RenanG0mes/GamepadPi/General pictures/1.jpg

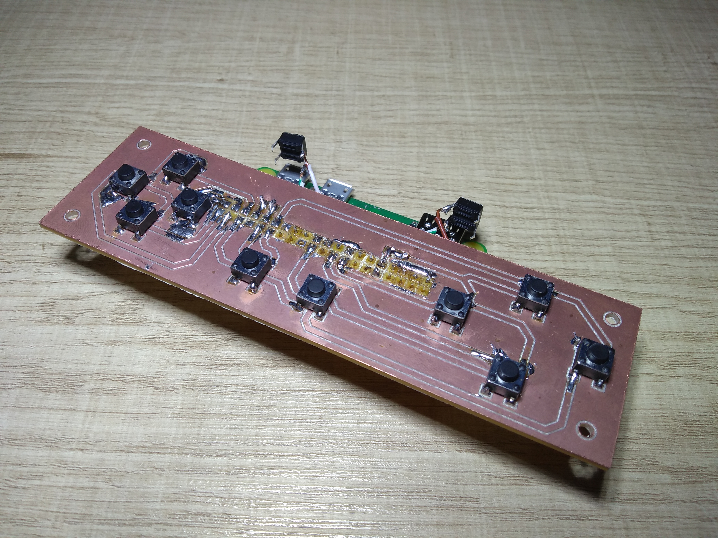
General pictures/1.jpg
