RenanG0mes/GamepadPi/General pictures/2.jpg

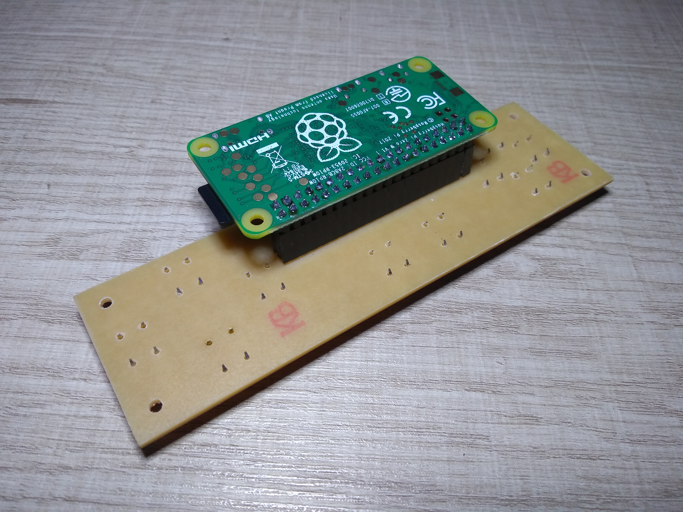
General pictures/2.jpg
