RenanG0mes/GamepadPi/General pictures/6.jpg

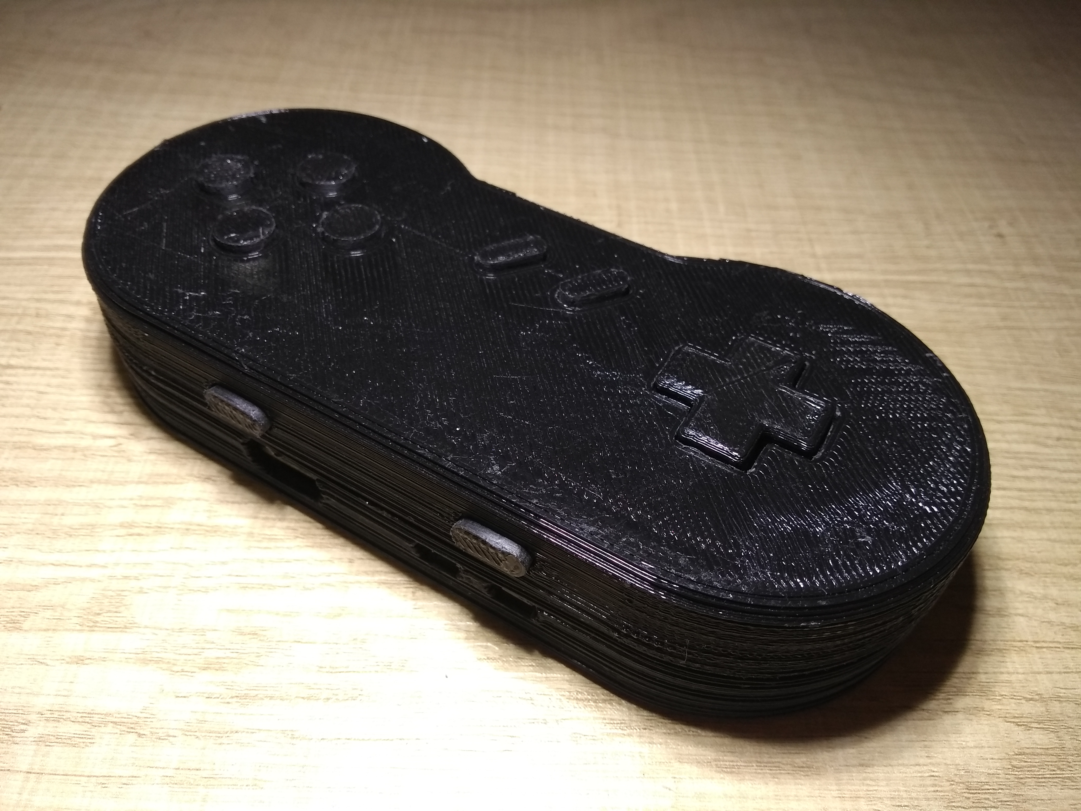
General pictures/6.jpg
