RenanG0mes/GamepadPi/General pictures/7.jpg

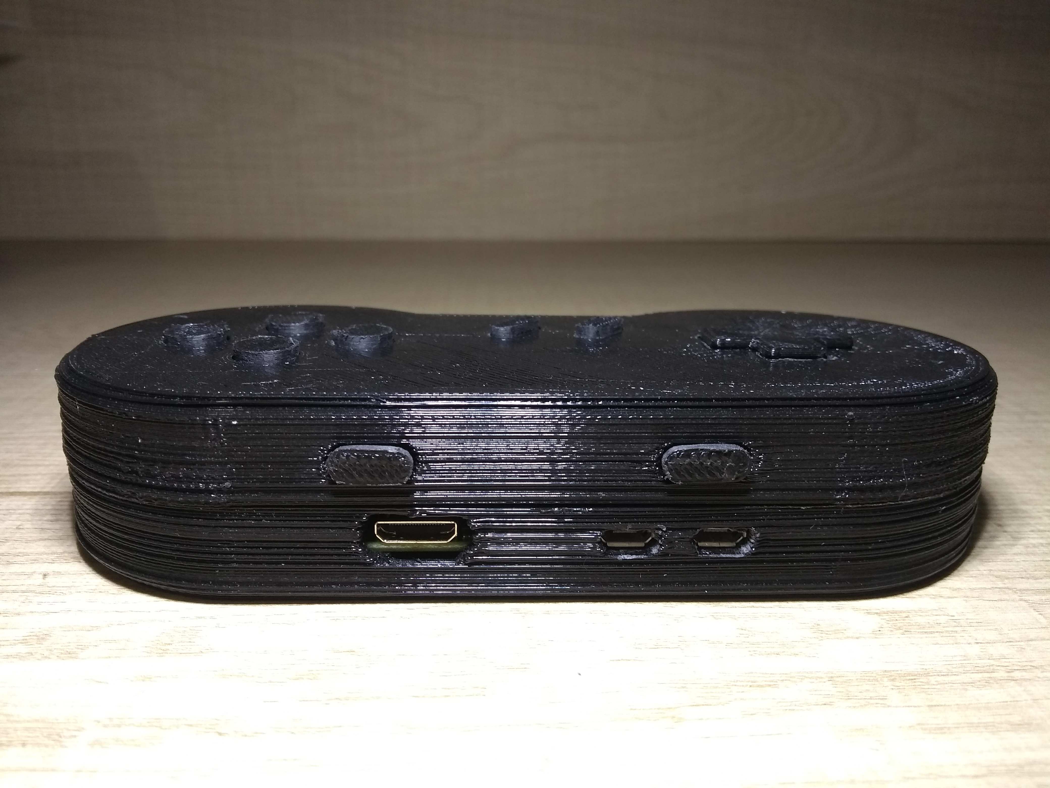
General pictures/7.jpg
