RenanG0mes/GamepadPi/General pictures/8.jpg

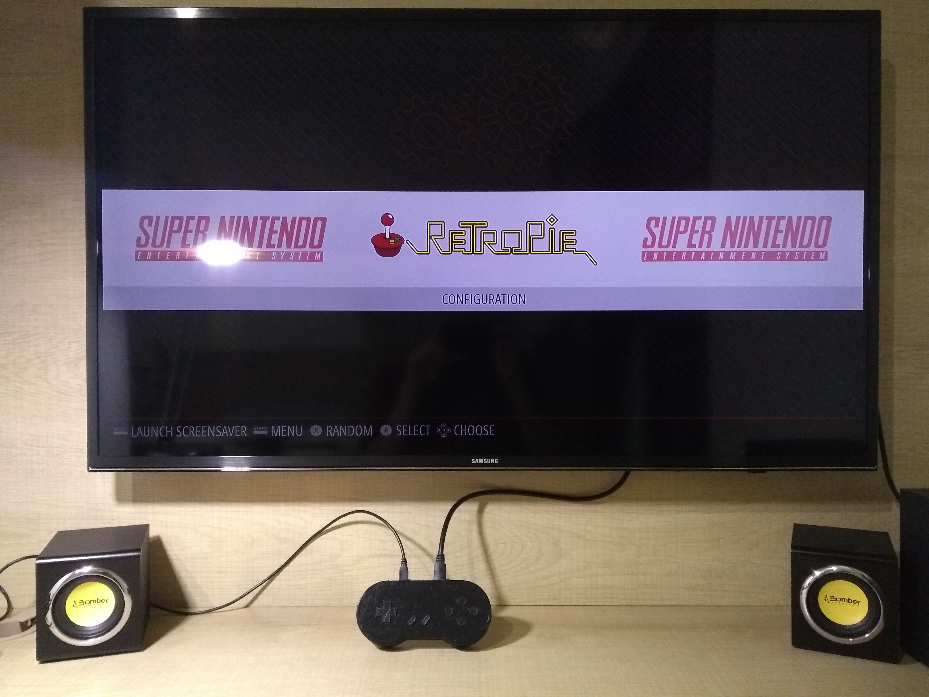
General pictures/8.jpg
