RenanG0mes/GamepadPi/General pictures/9.jpg

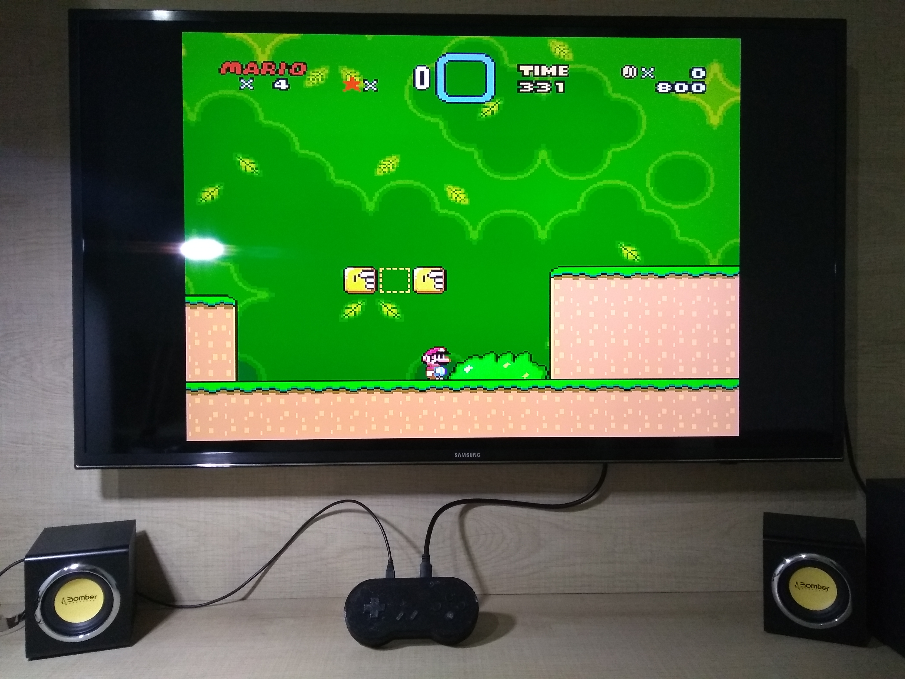
General pictures/9.jpg
