RenanG0mes/GamepadPi/General pictures/10.jpg

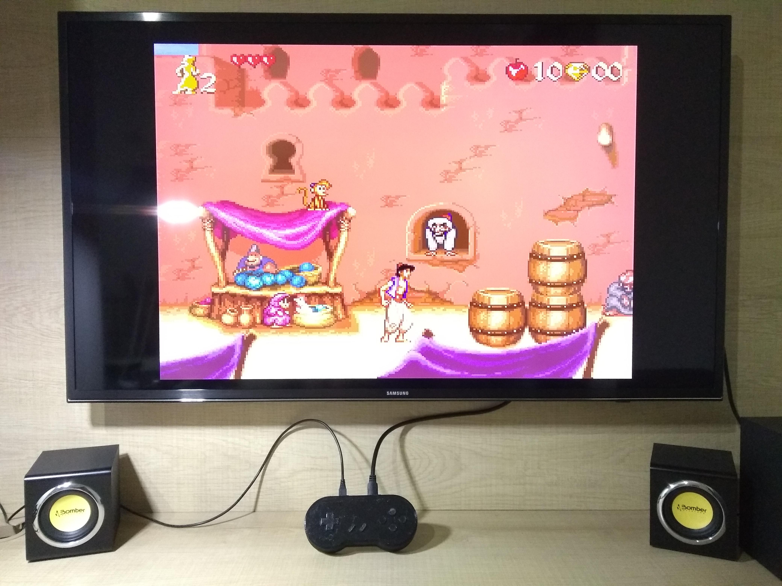
General pictures/10.jpg
